Scorch1262/Datenlogger-MK1/DataLogMK1v4.0.X/command.c

/*
 * File:   command.c
 * Author: Torben
 *
 * Created on October 6, 2020, 9:35 AM
 */

/** Includes **************************************************/
#define FCY 32000000UL

#include <xc.h>
#include <assert.h>
#include <stdbool.h>
#include <libpic30.h>
#include "mcc_generated_files/system.h"
#include "mcc_generated_files/mcc.h"
#include <string.h>
#include <stdio.h>
#include "command.h"
#include "mcp3221.h"
#include "mcp79410.h"
#include "lps33hw.h"

#if defined(__dsPIC33E__)
	#include <p33exxxx.h>
#elif defined(__dsPIC33F__)
	#include <p33fxxxx.h>
#elif defined(__dsPIC30F__)
	#include <p30fxxxx.h>
#elif defined(__PIC24E__)
	#include <p24exxxx.h>
#elif defined(__PIC24H__)
	#include <p24hxxxx.h>
#elif defined(__PIC24F__) || defined(__PIC24FK__)
	#include <p24fxxxx.h>
#endif

I2C1_MESSAGE_STATUS status;                                             // 

uint8_t  writeBuffer[3] = {0x00, 0x00, 0x00};                           // definiert "writeBuffer"
uint8_t  readBuffer[2] = {0x00, 0x00};                                  // definiert "readBuffer" 

uint8_t Slave_Address;                                                  // definiert "Slave_Address" 

uint16_t retryTimeOut1;                                                  // definiert "retryTimeOut1" 
uint16_t retryTimeOut2;                                                  // definiert "retryTimeOut2" 

/** Programm **************************************************/
void i2c1_message_pending_100(void){                                    // "i2c1_message_pending_100"
    retryTimeOut1 = 0;                                                  // setzt "retryTimeOut1" auf 0
    retryTimeOut2 = 0;                                                  // setzt "retryTimeOut2" auf 0
    while(status == I2C1_MESSAGE_PENDING){                              // solange "status" gleich "I2C1_MESSAGE_PENDING" ist
        if (retryTimeOut2 == 500){                                      // wenn "retryTimeOut2" gleich 100 ist
            break;                                                      // Abbruch der Schleife
        }else{                                                          // sonst
            retryTimeOut2++;                                            // "retryTimeOut2" +1
        }                                                               // 
    }                                                                   // 
    while(status != I2C1_MESSAGE_FAIL){                                 // solange "status" nicht gleich "I2C1_MESSAGE_FAIL" ist
        if (retryTimeOut1 == 500){                                      // wenn "retryTimeOut1" gleich 100 ist
            break;                                                      // Abbruch der Schleife
        }else{                                                          // sonst
            retryTimeOut1++;                                            // "retryTimeOut1" +1
        }                                                               // 
    }                                                                   // 
    //I2C1_LOST_STATE
}                                                                       // 
